Jay-Tai/Custom-Keyboard/journaling/major updates/schematic/readme.md

# Schematic
The schematic includes all the components of my keyboard!  
The keyboard includes all the correct wiring for the backlights, the switches, the Display, and the Rotary Encoder that is going to be part of the final keyboard.  

I acutally got really lucky with the microcontroller - I had JUST ENOUGH ports to house all the different pins that everything in my keyboard requires.  

Take a look at the schematic image in the folder, and the timelapse here!: https://canva.link/jdkn7mn0ot2y70i
