Jay-Tai/Custom-Keyboard/journaling/(almost) daily journaling/July 24, 2026/readme.md

<p><b>Finshing the keyboard keymap</b></p>
<p><i>1 hour and 6 minutes logged</i></p>

Today, I finished the keymap of my keyboard, and I am onto the rotary encoder! However, I am constantly facing errors, and I am pushing through that!
