Jay-Tai/Custom-Keyboard/journaling/(almost) daily journaling/July 21, 2026/readme.md

<p><b>2nd day of my firmware!</b></p>
<p><i>1 hour and 41 minutes logged</i></p>

Today, I was writing my firmware again!
For some reason, it didn't save my work yesterday, so I redid it (For 25 minutes), and I finished the encoder and configured the lights so far!
Excited for tomorrow!
