Jay-Tai/Custom-Keyboard/journaling/(almost) daily journaling/July 20, 2026/readme.md

<p><b>Starting the firmware!</b></p>
<p><i>1 hour and 21 minutes logged</i></p>

Today, I started the firmware for my keyboard! I laid out all of the functions of the keys, and I programmed all of them. I also created the macro for the mute/unmute function of the rotary encoder wheToday, I started the firmware for my keyboard! I laid out all of the functions of the keys, and I programmed all of them. I also created the macro for the mute/unmute function of the rotary encoder when I press it in meetings.
Tomorrow, I will be programming the lights and the screen. From there, I am going to do the final touches, create the BOM, and then end a chapter!
Here is the code so far!
