Jay-Tai/Custom-Keyboard/journaling/(almost) daily journaling/July 18, 2026/readme.md

<p><b>Started the CAD!</b></p>
<p><i>1 hour and 9 minutes logged</i></p>

Today, I started my CAD! I made the main base, along with a spot to put in my PCB. here's what it looks like so far! :D
