Jay-Tai/Custom-Keyboard/journaling/(almost) daily journaling/July 17, 2026/readme.md

<p><b>Finished the PCB!</b></p>
<p><i>1 hour and 4 minutes logged</i></p>

Today, I finished up my PCB! I made a ground plane, and I used the Vias that I learnt about yesterday to make clean wiring for my keyboard.
Here's what it looks like!



(The random background is the ground plane)
