Jay-Tai/Custom-Keyboard/journaling/(almost) daily journaling/July 16, 2026/readme.md

<p><b>Big breakthrough</b></p>
<p><i>1 hour and 14 minutes logged</i></p>

Today, I had to clear out all of my work again, but I learnt what vias are, and how to make them, along with making a VCC plane to help me finally finish these LEDs! I will be doing that tomorrow.
Here's a look at one of my vias that I am going to be connecting to a plane from a capacitor.
