Jay-Tai/Custom-Keyboard/journaling/(almost) daily journaling/July 15, 2026/readme.md

<p><b>Fixing wiring</b></p>
<p><i>1 hour and 3 minutes logged</i></p>

Today, I ended up deleting all of the previous vias I made for my PCB's lights, and ended up starting all over again. Here is a look!
