Jay-Tai/Custom-Keyboard/journaling/(almost) daily journaling/July 12, 2026/readme.md

<p><b>Starting the CAD!</b></p>
<p><i>1 hour and 17 minutes logged</i></p>

Today, I started the CAD! I didn't get far, as I was getting very distracted, and still getting in the jist of things. In addition, I also wasn't at home or at my computer for a long portion of today.
