Jay-Tai/Custom-Keyboard/journaling/(almost) daily journaling/July 11, 2026/readme.md

<p><b>Finished the PCB!</b></p>
<p><i>5 hours and 36 minutes logged</i></p>

Today, I finished my PCB!
I worked on the silkscreen and made that the rest of the PCB was in function
