Jay-Tai/Custom-Keyboard/journaling/(almost) daily journaling/July 9, 2026/readme.md

<p><b>Keyboard Silkscreen Work</b></p>
<p><i>1 hour and 3 minutes logged</i></p>

Today, I worked on the keyboard's Silkscreen! I am making a topographic layer, and I finished the rough idea of how it will look like!
Tomorrow, I will be cleaning up the effect, and then adding it to my project!
This is what the silkscreen looks like so far! :D
