Jay-Tai/Custom-Keyboard/journaling/(almost) daily journaling/July 8, 2026/readme.md

<p><b>Small update</b></p>
<p><i>1 hour and 5 minutes logged</i></p>

Today was a bit of just a small progress day. I finished the wiring, and fixed an error with my rotary encoder.



I also learnt how to make silkscreens!
