Jay-Tai/Custom-Keyboard/journaling/(almost) daily journaling/July 7, 2026/readme.md

<p><b>Finished wiring!</b></p>
<p><i>3 hours and 5 minutes logged</i></p>

Today, I finished up all of the wiring for my project, fixed any errors, and also finished 90% of the wiring for the switches!
Here's a quick photo of it! :D


Tomorrow, I am going to finish my PCB, and start the case!
IM SO EXCITEDDDD
