Jay-Tai/Custom-Keyboard/journaling/(almost) daily journaling/July 6, 2026/readme.md

<p><b>Finishing layout + starting wiring</b></p>
<p><i>3 hours and 32 minutes logged</i></p>

Today, I finished the layout of my entire project and started wiring! I finished the power and GND of all LEDs, and I am working on DIN and DOUT!
