Jay-Tai/Custom-Keyboard/journaling/(almost) daily journaling/July 5, 2026/readme.md

<p><b>Electric component layout</b></p>
<p><i>2 hours and 2 minutes logged</i></p>

Today, I worked on figuring out electrical component layout, along with placing the arrow keys + top row of my keyboard (Along with all of its electrical components, such as a Capacitor!)
Take a look at the image!
