Jay-Tai/Custom-Keyboard/journaling/(almost) daily journaling/July 4, 2026/readme.md

<p><b>Assigning footprints!</b></p>
<p><i>2 hours and 3 minutes logged</i></p>

Today was a bit of a busy day for me. However, for my custom keyboard, I still managed to work on assigning my footprints!
I forgot to record part of it. Sorry! :P
I faced a bit of an error where KiCad kept on crashing every single time I tried opening the "Assign Footprints" window. I  spent around 2 hours on that!
