Jay-Tai/Custom-Keyboard/journaling/(almost) daily journaling/July 3, 2026/readme.md

<p><b>My KiCad Schematic!</b></p>
<p><i>4 hours and 27 minutes logged</i></p>
<p>(Yes, it was all done in a day haha)</p>

The schematic includes all the components of my keyboard!
The keyboard includes all the correct wiring for the backlights, the switches, the Display, and the Rotary Encoder that is going to be part of the final keyboard.
I acutally got really lucky with the microcontroller - I had JUST ENOUGH ports to house all the different pins that everything in my keyboard requires.

<i>Take a look at the final shematic!</i>
<br/>
The final schematic!

Watch the timelapse here:
https://f8d710a55cb9b516d88635f103c2c9f2.r2.cloudflarestorage.com/collapse/timelapses/5871cd09-b832-4ddf-aae9-c32493282611/timelapse.mp4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
