Jay-Tai/Custom-Keyboard/journaling/major updates/final shell/readme.md

# The final shell!
Today, I finished up the shell for the keyboard! This was really fun to make, and it took ~w2.5 hours to make the entire thing.

Here is what the shell looks like without the PCB:
<br/>
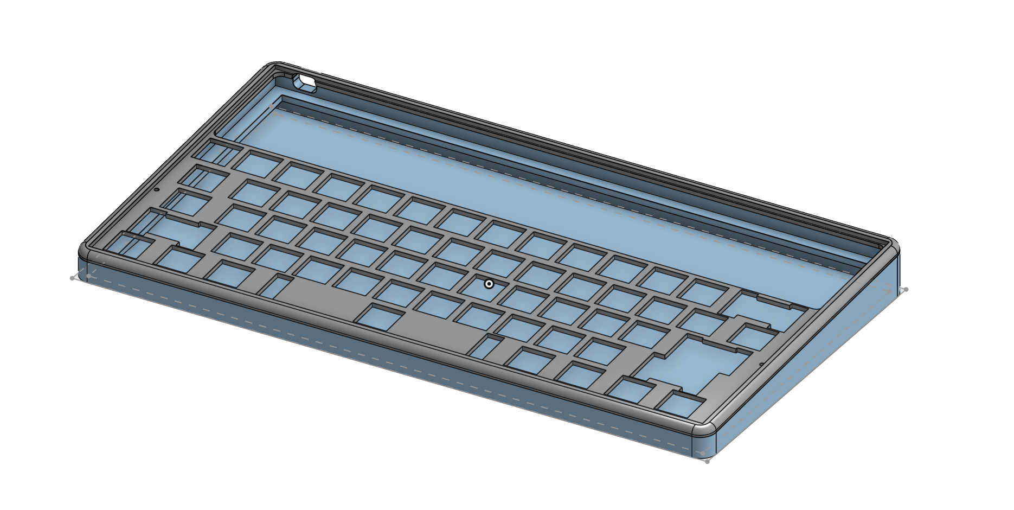
[picture p10: journaling/major updates/final shell/assets/1.png]


Here is what the PCB looks like without the shell:
<br/>
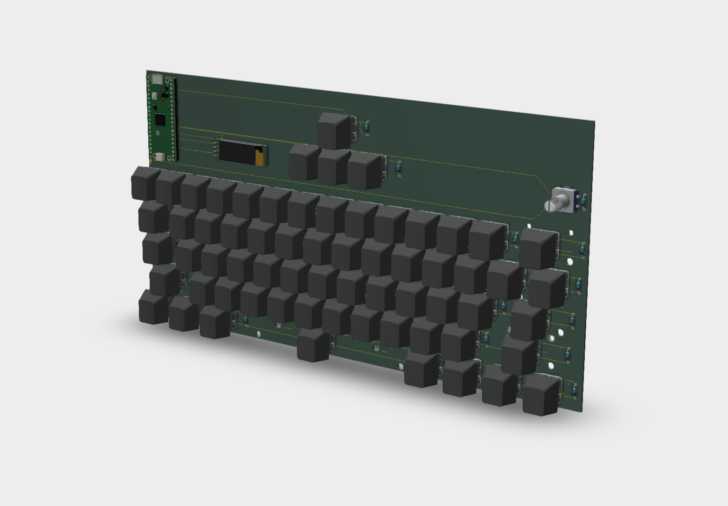
[picture p11: journaling/major updates/final shell/assets/2.png]


Here is what the shell looks like with the PCB:
<br/>
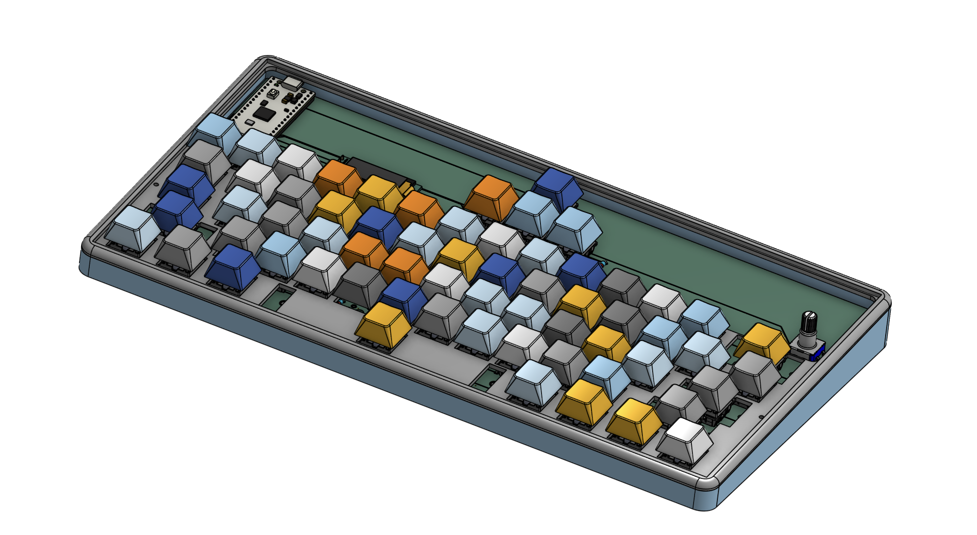
[picture p12: journaling/major updates/final shell/assets/3.png]
