Jay-Tai/Custom-Keyboard/journaling/major updates/final pcb fault fix/readme.md

After I made my last journal entry, I faced an issue: the LEDs on my PCB are in the wrong direction.
I spent a lot of time figuring out how to rewire the LEDs to be for the bottom, and restarted its wiring a grand total of 7 times.

This was until I learnt what <b>vias</b> are.

I used vias several times to "jump" wiringto actually make this work!

Yesterday, I finished the PCB :D!! Here is what it looks like:

My PCB!
