Jay-Tai/Custom-Keyboard/journaling/major updates/final pcb/readme.md

# Final PCB Update
I have finished the final PCB! In my opinion, it looks awesome. I love the silkscreen, and how organized everything is!

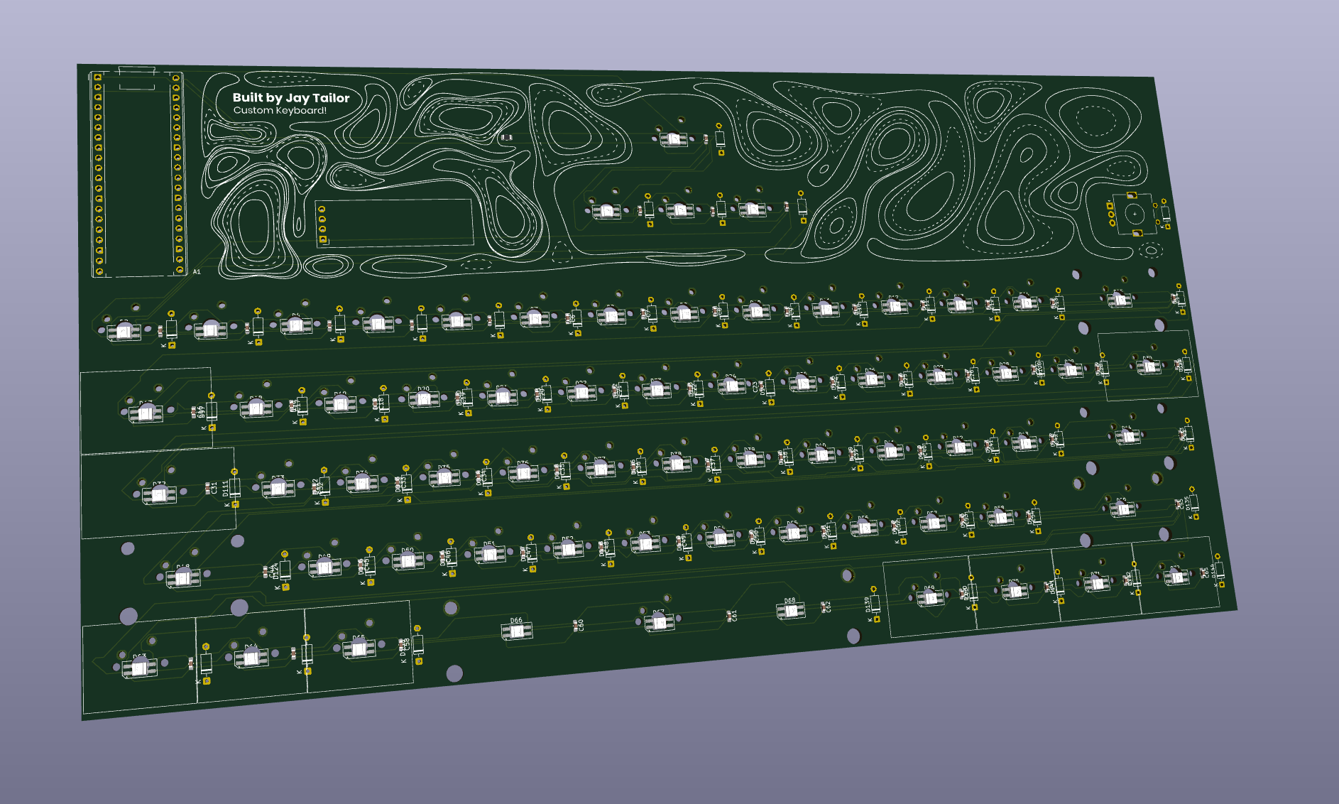
[picture p13: journaling/major updates/final pcb/image_1.png]
IT LOOKS AWESOME!!

Doesn't it look amazing?

Here is what it looks like in the KiCad PCB Editor
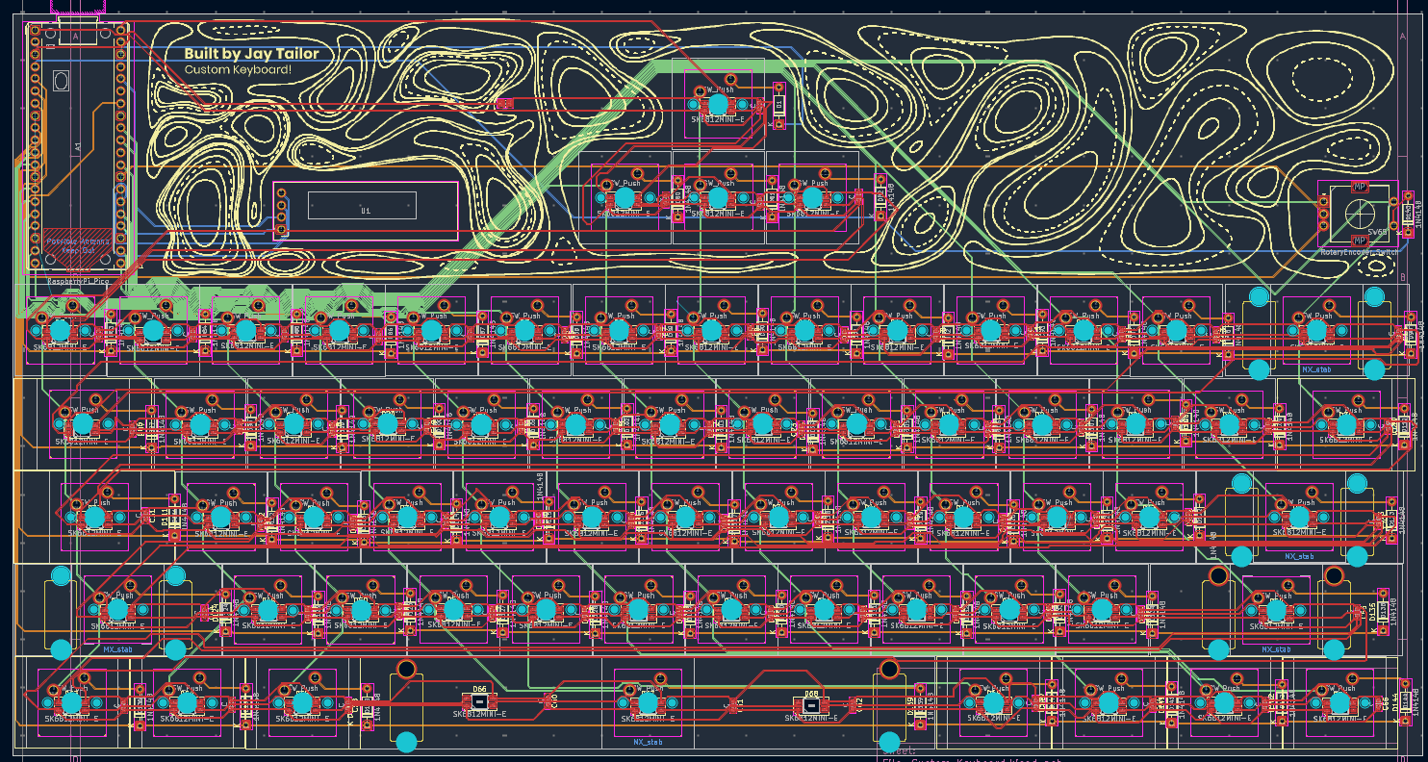
[picture p14: journaling/major updates/final pcb/image_2.png]
Idk what to put here
