Jay-Tai/Custom-Keyboard/journaling/major updates/underlight/readme.md

Finished the underlights! Took around 8 hours to place all the items for the PCB, and wire the lights!

Next is to wire the switches!
