Jay-Tai/Custom-Keyboard/journaling/major updates/sketching/readme.md

# Sketching
Sketching is the most important component of any project - I visualized the design of my keyboard on paper. Take a look at the timelapse and the sketch image!
